PhysicsUofRAUI/binTempSensor/how_to_docs/photos/flat_antenna.jpg

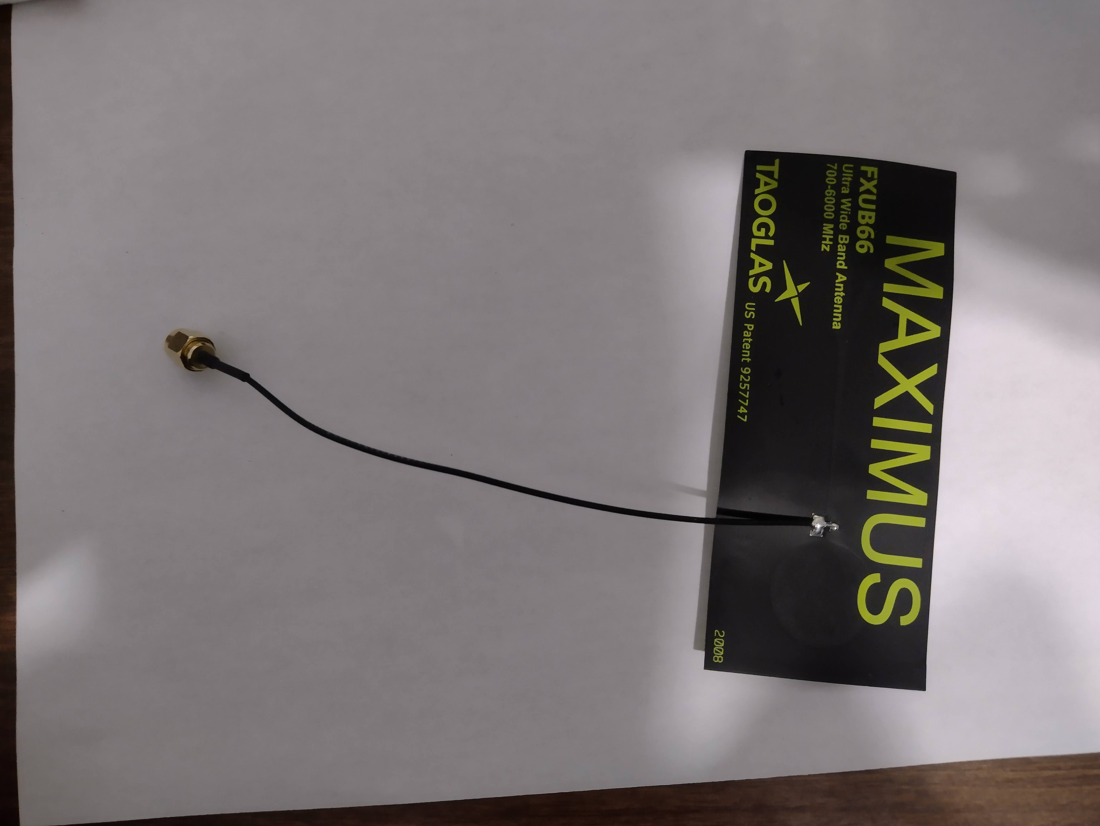
how_to_docs/photos/flat_antenna.jpg
