PhysicsUofRAUI/binTempSensor/how_to_docs/photos/magnetic_antenna.jpg

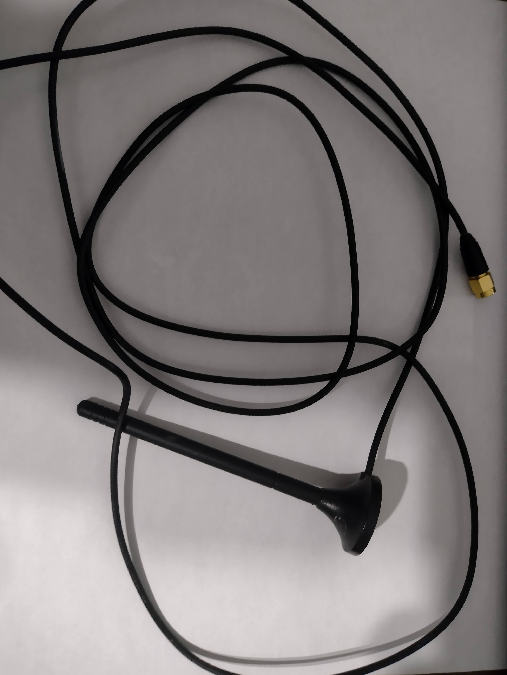
how_to_docs/photos/magnetic_antenna.jpg
